qtechdesign/qtech/FPS/tools/app/FrostProtectionSystem_IOS-develop/FrostProtectionSystem_IOS/Resources/Assets.xcassets/Drawer Navigation/ic_router.imageset/ic_router.pdf

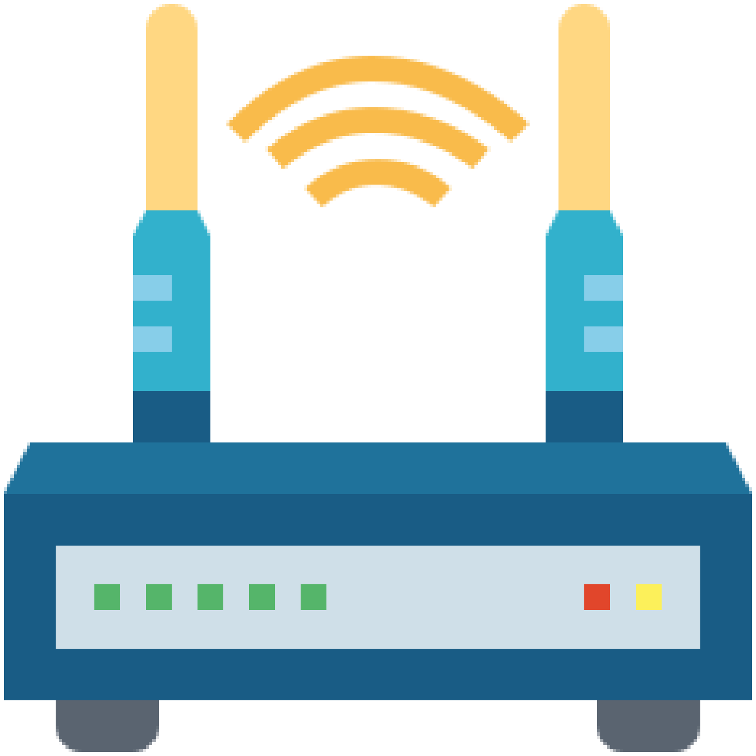
[picture p3: page 1]
