qtechdesign/qtech/FPS/tools/app/FrostProtectionSystem_IOS-develop/FrostProtectionSystem_IOS/Resources/Assets.xcassets/Home/ic_qr_code_default.imageset/ic_qr_code_default.pdf

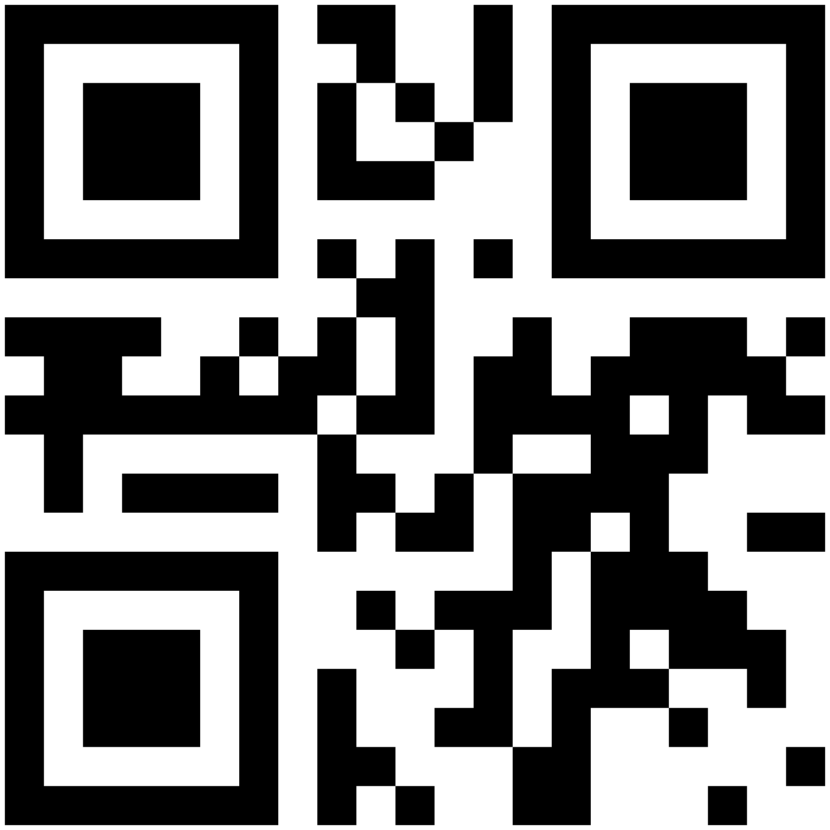
[picture p4: page 1]
