qtechdesign/qtech/FPS/tools/app/FrostProtectionSystem_IOS-develop/FrostProtectionSystem_IOS/Resources/Assets.xcassets/Main/ic_logo_blue.imageset/ic_logo_blue.pdf

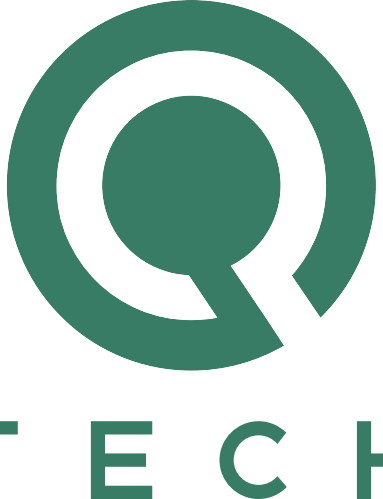
[picture p5: figure]
