qtechdesign/qtech/FPS/tools/app/FrostProtectionSystem_IOS-develop/FrostProtectionSystem_IOS/Resources/Assets.xcassets/Main/logo.imageset/logo.pdf

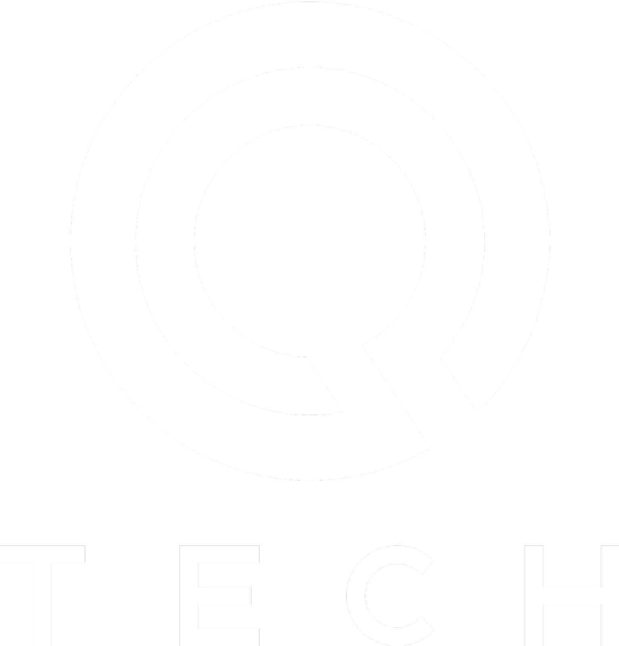
[picture p6: page 1]
