qtechdesign/qtech/FPS/tools/app/FrostProtectionSystem_IOS-develop/FrostProtectionSystem_IOS/Resources/Assets.xcassets/Map/ic_gateway_marker.imageset/ic_gateway_marker.pdf

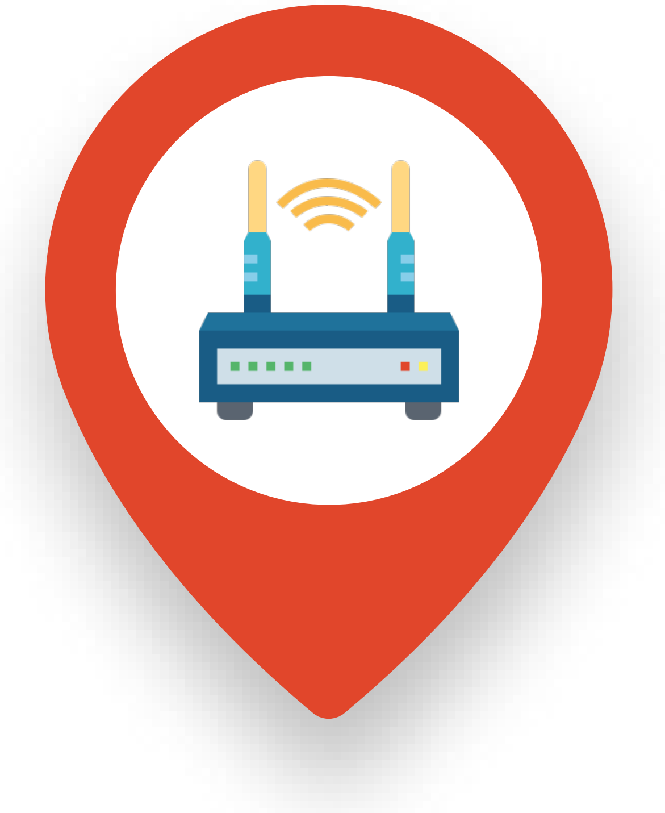
[picture p7: page 1]
