qtechdesign/qtech/FPS/tools/app/FrostProtectionSystem_IOS-develop/FrostProtectionSystem_IOS/Resources/Assets.xcassets/Map/ic_sensor_marker.imageset/ic_sensor_marker.pdf

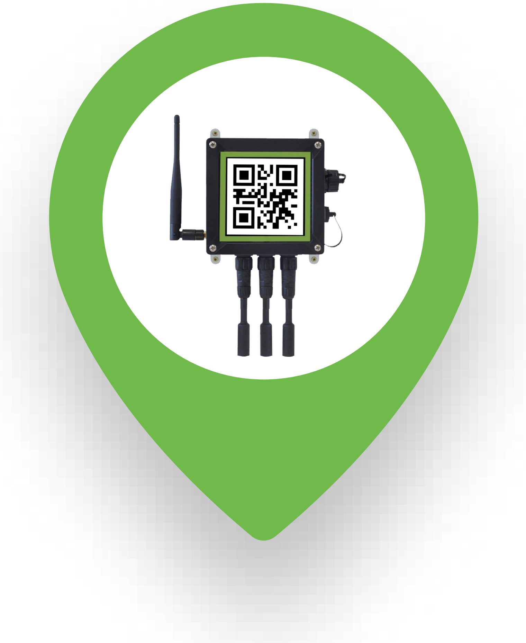
[picture p8: page 1]
