qtechdesign/qtech/FPS/tools/app/FrostProtectionSystem_IOS-develop/FrostProtectionSystem_IOS/Resources/Assets.xcassets/Map/ic_valve_marker.imageset/ic_valve_marker.pdf

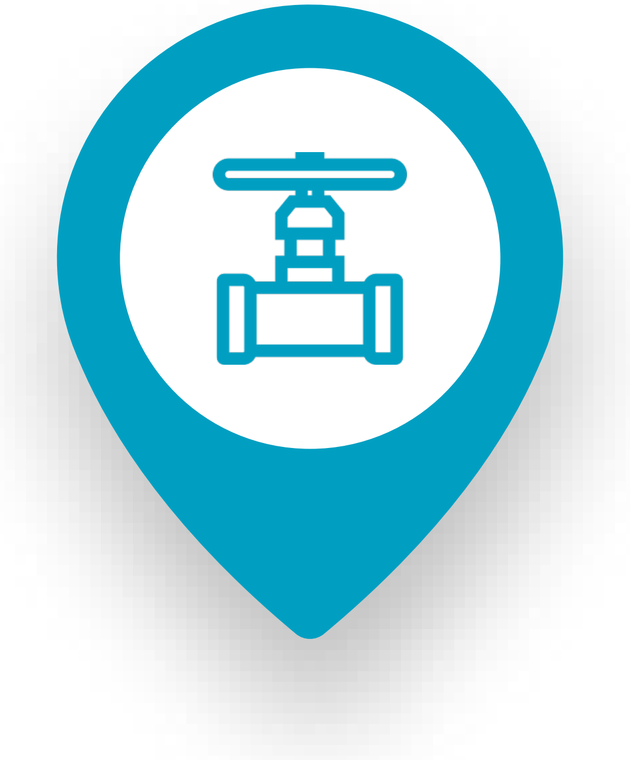
[picture p9: page 1]
