qtechdesign/qtech/FPS/tools/app/FrostProtectionSystem_IOS-develop/FrostProtectionSystem_IOS/Resources/Assets.xcassets/Sensor/ic_sensor_node.imageset/ic_sensor_node.pdf

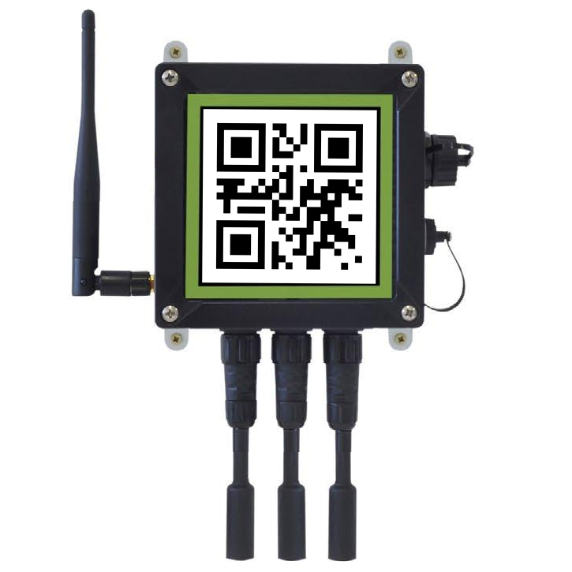
[picture p10: page 1]
