qtechdesign/qtech/FPS/tools/app/FrostProtectionSystem_IOS-develop/FrostProtectionSystem_IOS/Resources/Assets.xcassets/Sensor/ic_valve_close.imageset/ic_valve_close.pdf

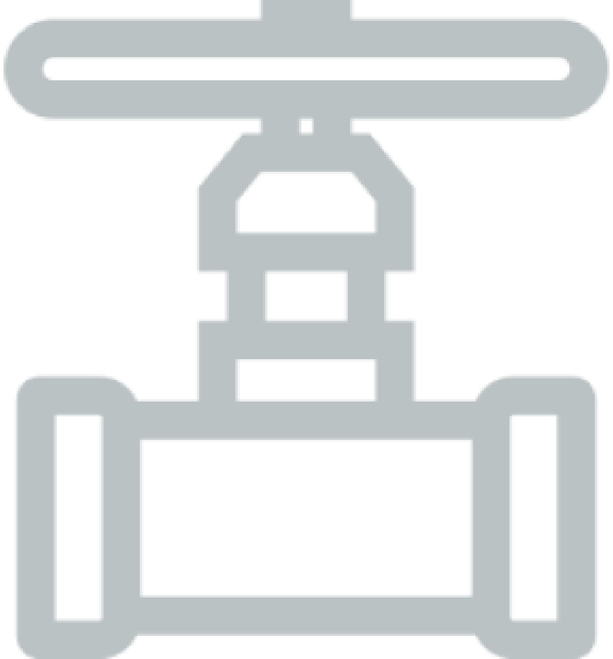
[picture p11: page 1]
