qtechdesign/qtech/FPS/tools/app/FrostProtectionSystem_IOS-develop/FrostProtectionSystem_IOS/Resources/Assets.xcassets/Sensor/ic_valve_open.imageset/ic_valve_open.pdf

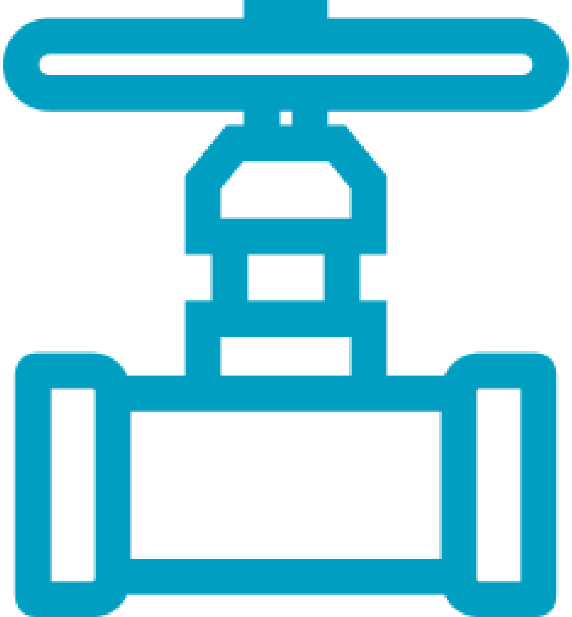
[picture p12: page 1]
