qtechdesign/qtech/FPS/tools/app/FrostProtectionSystem_IOS-develop/FrostProtectionSystem_IOS/Resources/Assets.xcassets/Sensor/ic_valves_node.imageset/ic_valves_node.pdf

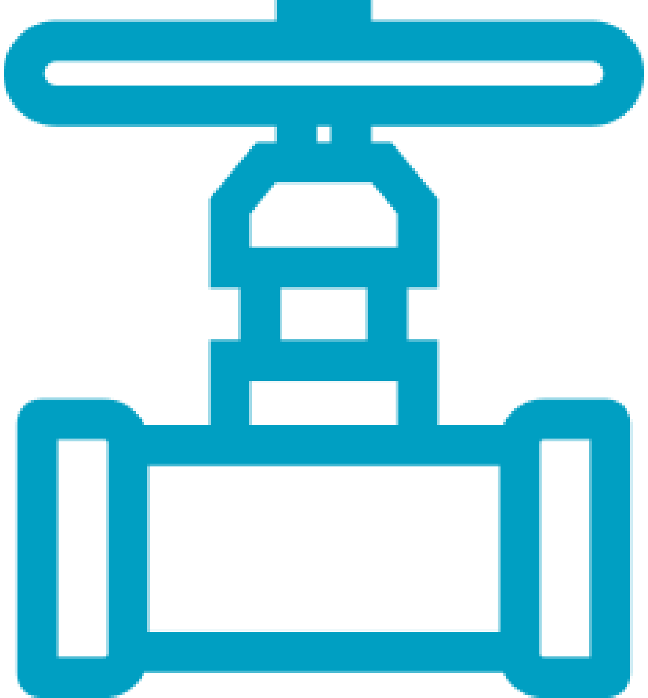
[picture p13: page 1]
